Petersoj/FSSPrototype/assets/Schematics and PCB Layouts/Breakout Board v1.0/PCB Layers/Hole.pdf

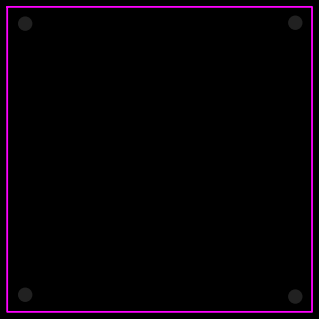
[picture p21: figure]
