Petersoj/FSSPrototype/assets/Schematics and PCB Layouts/Breakout Board v1.0/PCB Layers/Multi-Layer.pdf

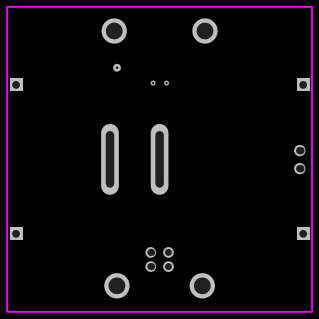
[picture p22: figure]
