Petersoj/FSSPrototype/assets/Schematics and PCB Layouts/Main Board v1.0/PCB Layers/Multi-Layer.pdf

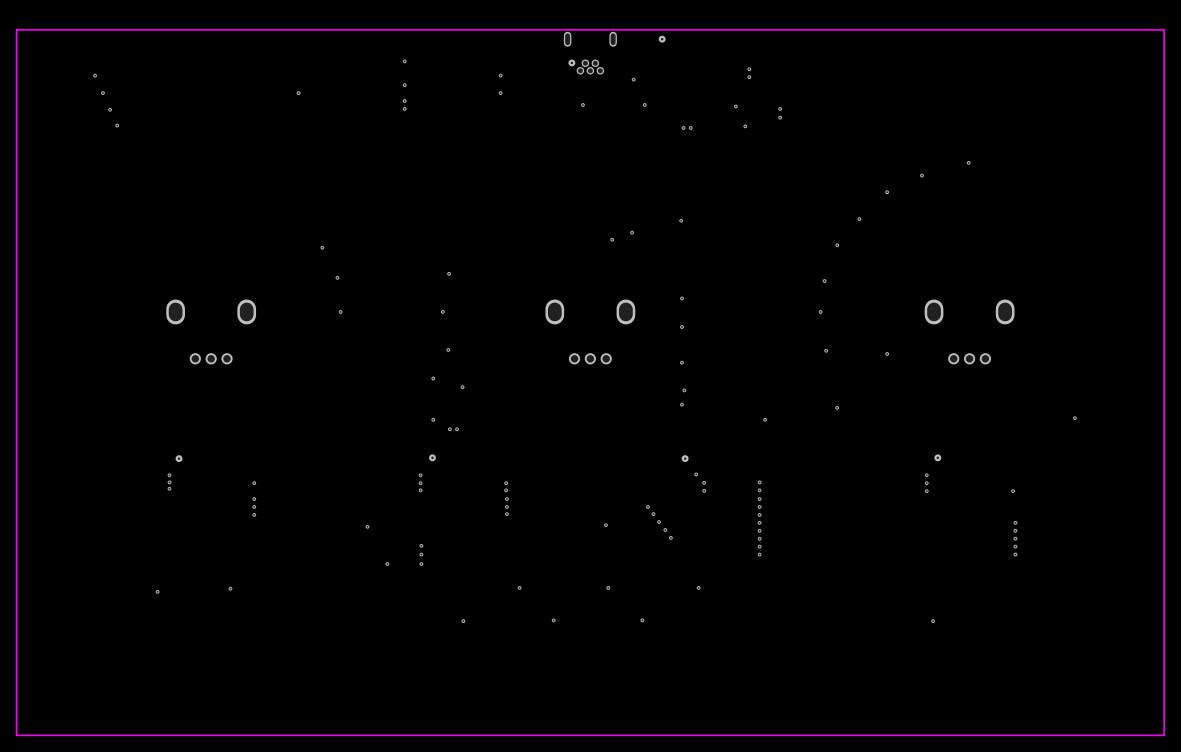
[picture p23: page 1]
