Petersoj/FSSPrototype/assets/Schematics and PCB Layouts/Main Board v1.0/PCB Layers/TopPasteMaskLayer.pdf

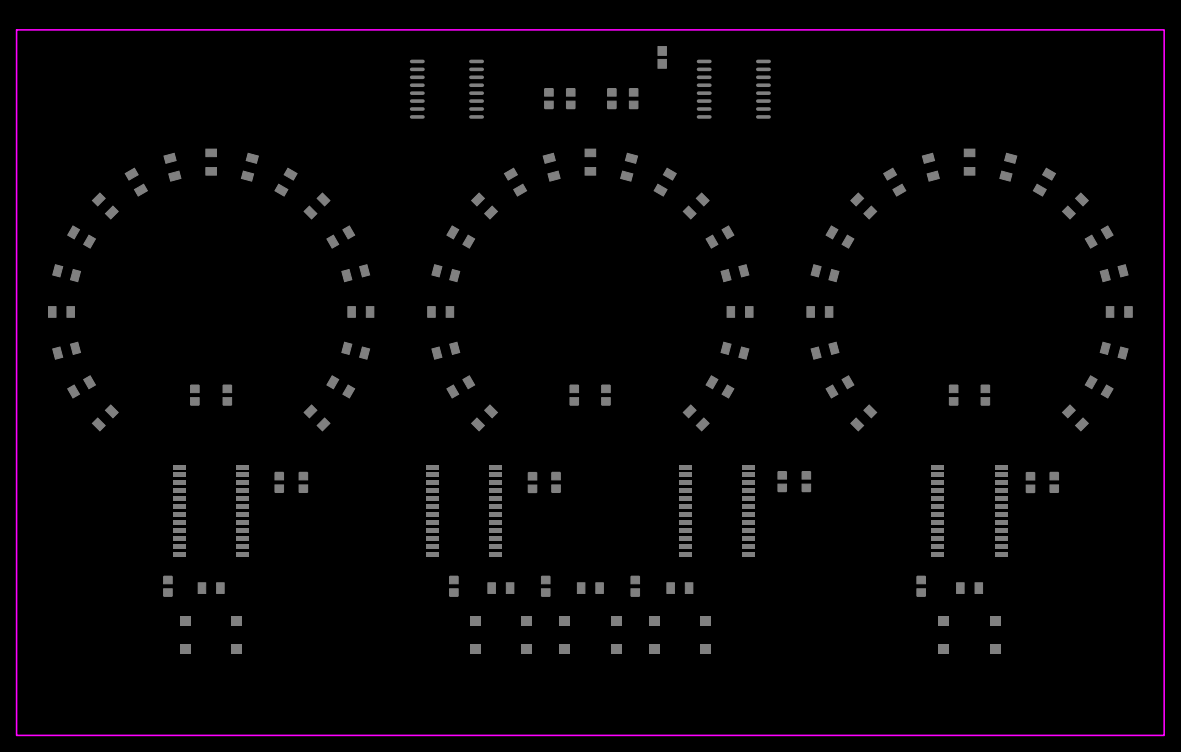
[picture p24: page 1]
