Petersoj/FSSPrototype/assets/Schematics and PCB Layouts/Breakout Board v1.0/PCB Layers/BottomSolderMaskLayer.pdf

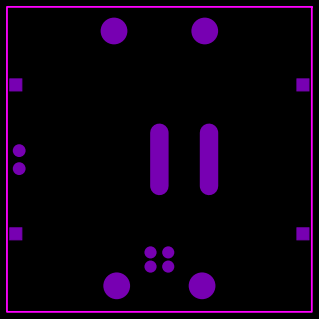
[picture p39: figure]
