Petersoj/FSSPrototype/assets/Schematics and PCB Layouts/Breakout Board v1.0/PCB Layers/TopSolderMaskLayer.pdf

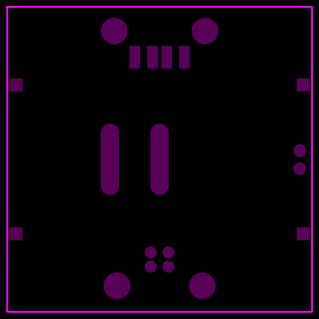
[picture p40: figure]
