Petersoj/FSSPrototype/assets/Schematics and PCB Layouts/Breakout Board v1.0/PCB Layers/BottomLayer.pdf

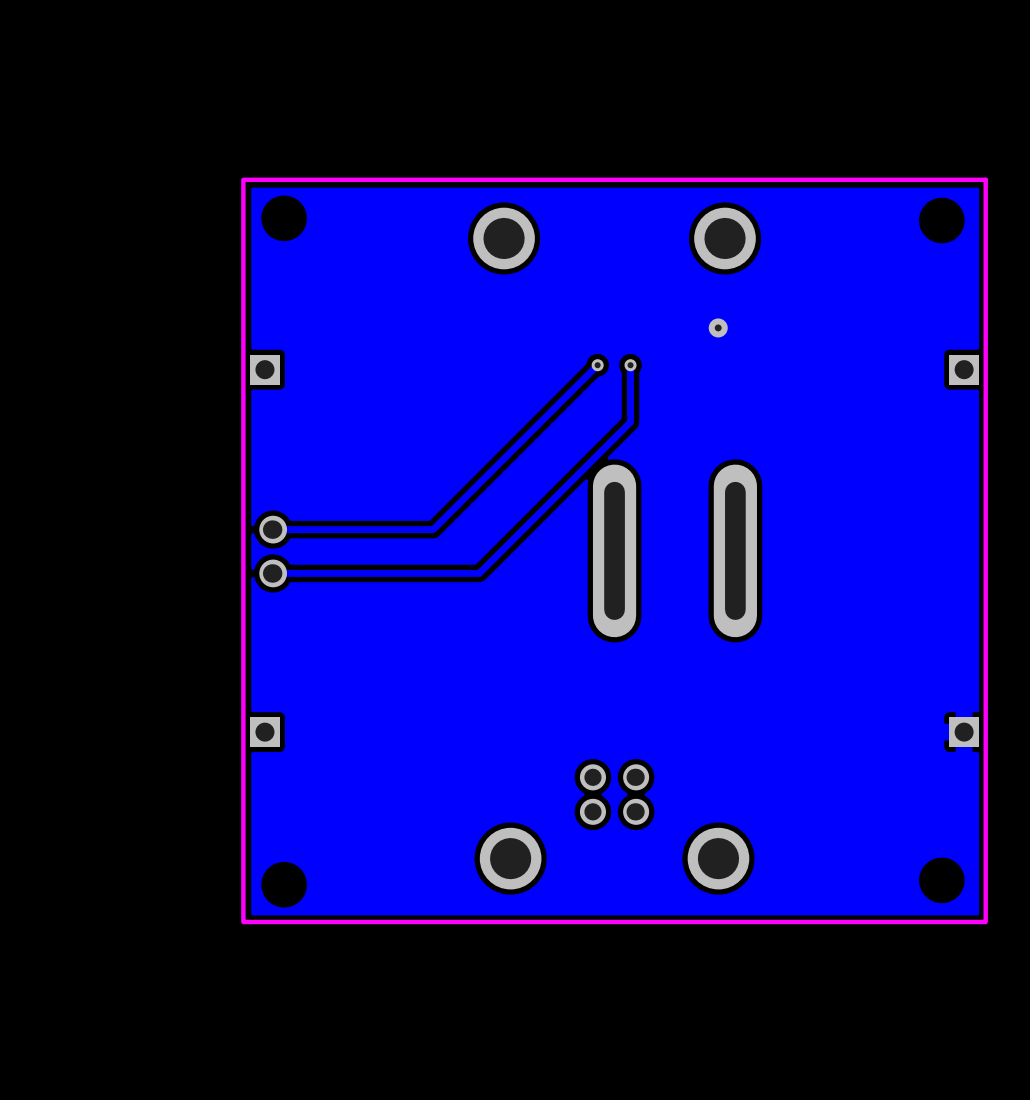
[picture p47: page 1]
