Petersoj/FSSPrototype/assets/Schematics and PCB Layouts/Breakout Board v1.0/PCB Layers/TopLayer.pdf

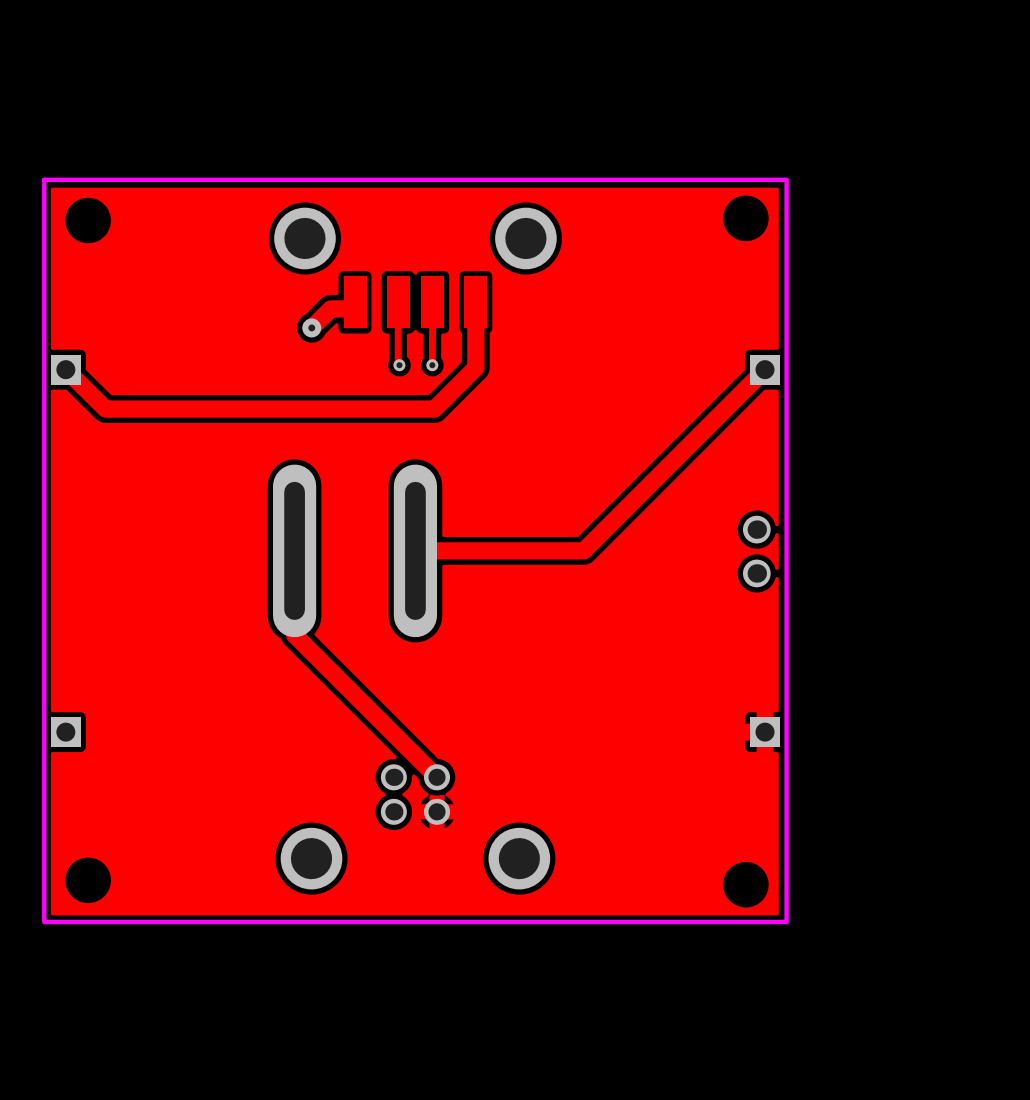
[picture p48: page 1]
