Petersoj/FSSPrototype/assets/Schematics and PCB Layouts/Breakout Board v1.0/PCB Layers/TopSilkLayer.pdf

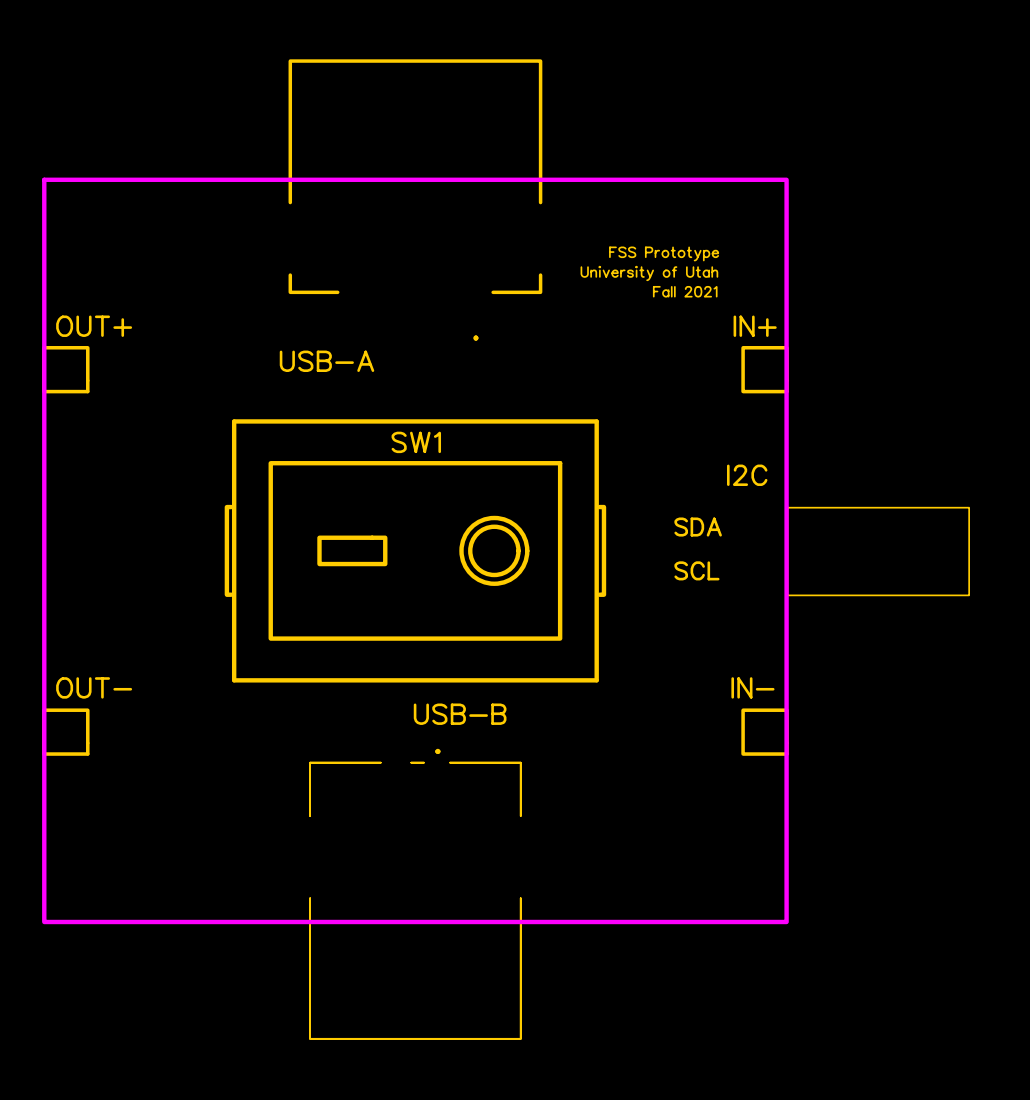
[picture p49: page 1]
