Petersoj/FSSPrototype/assets/Schematics and PCB Layouts/Main Board v1.0/PCB Layers/BottomLayer.pdf

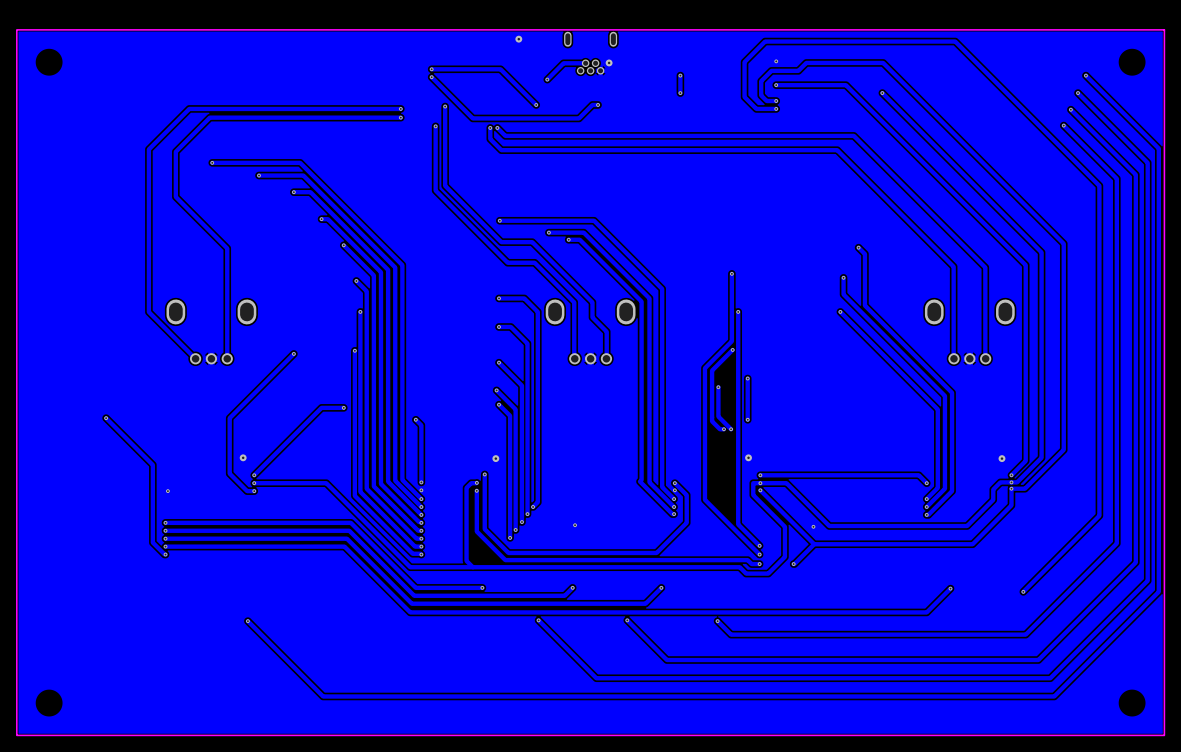
[picture p50: page 1]
