Petersoj/FSSPrototype/assets/Schematics and PCB Layouts/Main Board v1.0/PCB Layers/TopLayer.pdf

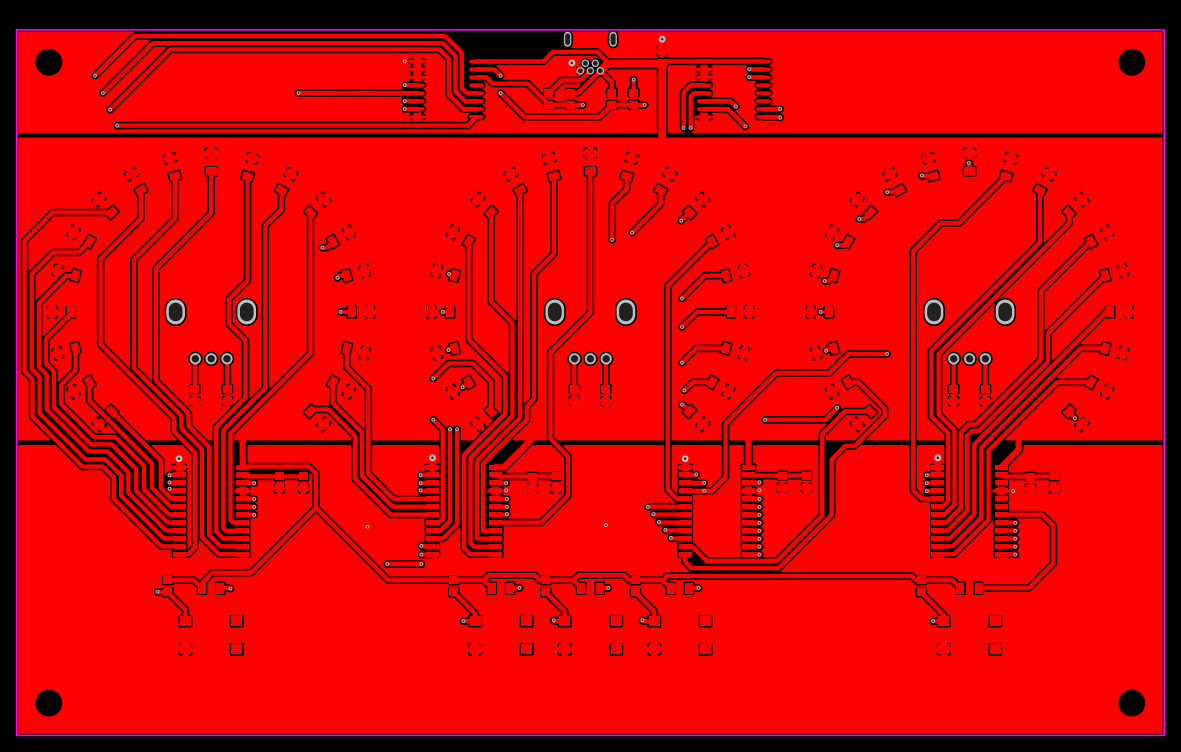
[picture p51: page 1]
