Petersoj/FSSPrototype/assets/Schematics and PCB Layouts/Main Board v1.0/PCB Layers/TopSilkLayer.pdf

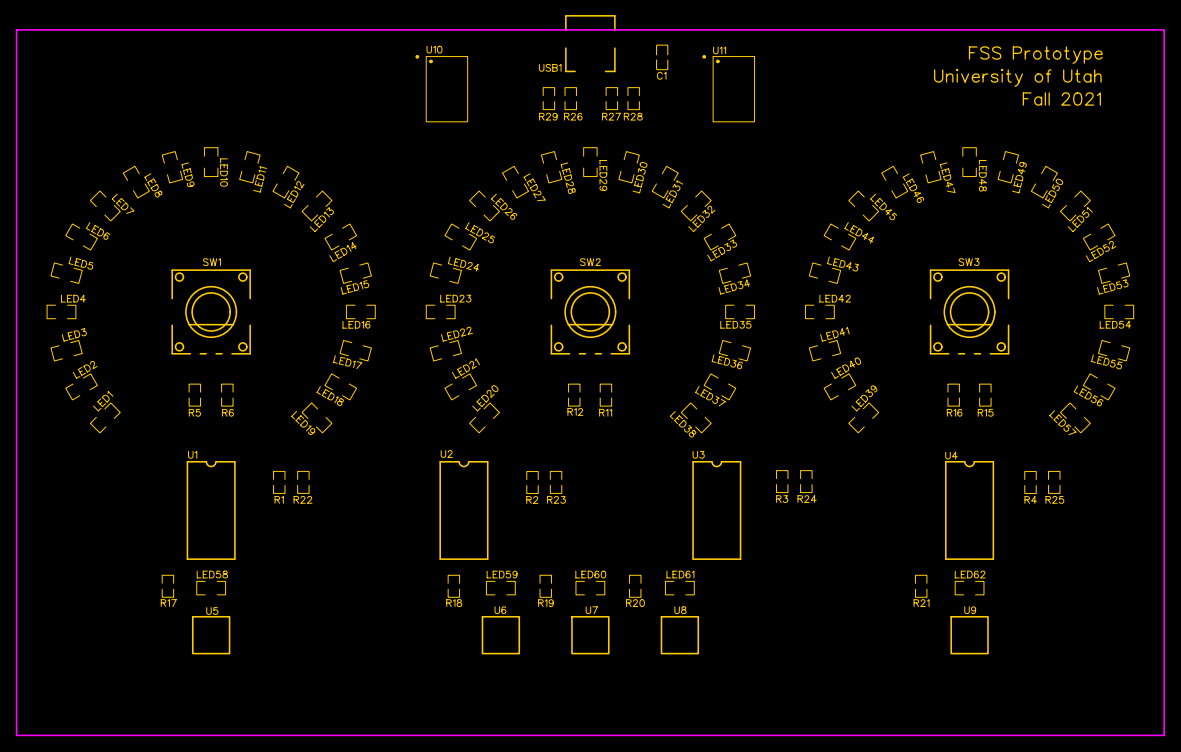
[picture p52: page 1]
