Petersoj/FSSPrototype/assets/Schematics and PCB Layouts/Main Board v1.0/PCB Layers/TopSolderMaskLayer.pdf

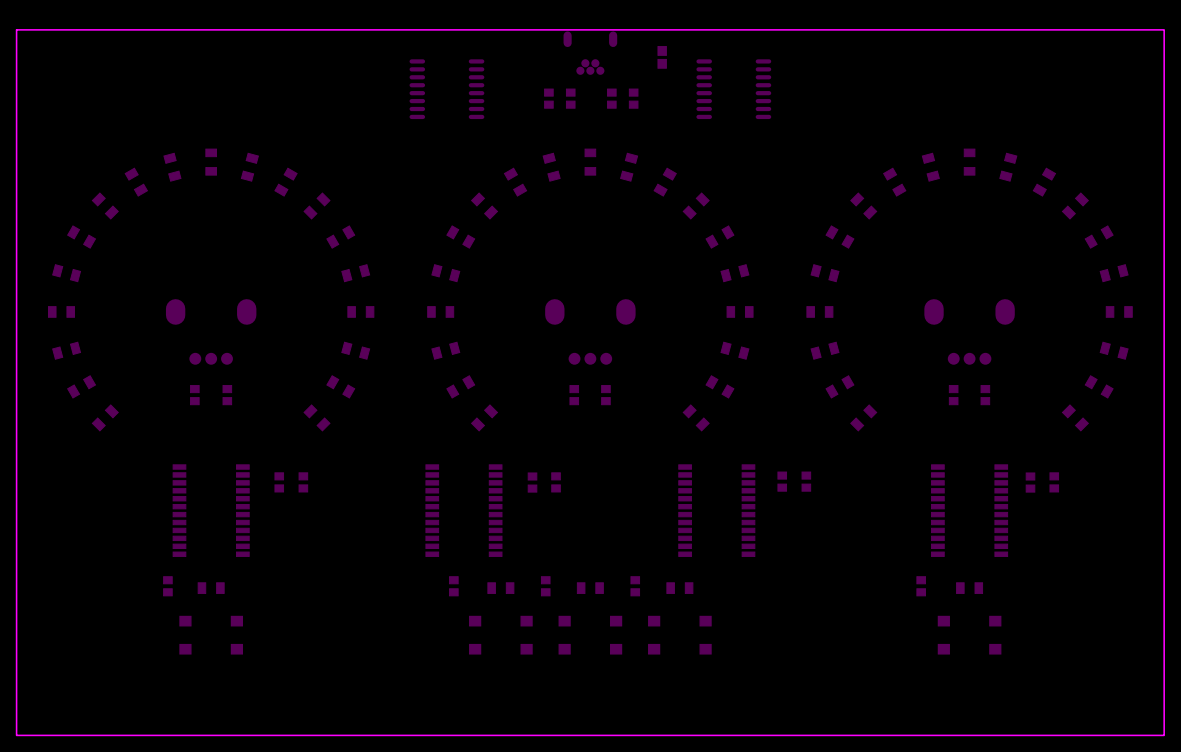
[picture p53: page 1]
