Petersoj/FSSPrototype/docs/Reports/Final Report/resources/figures/breakout_pcb.pdf

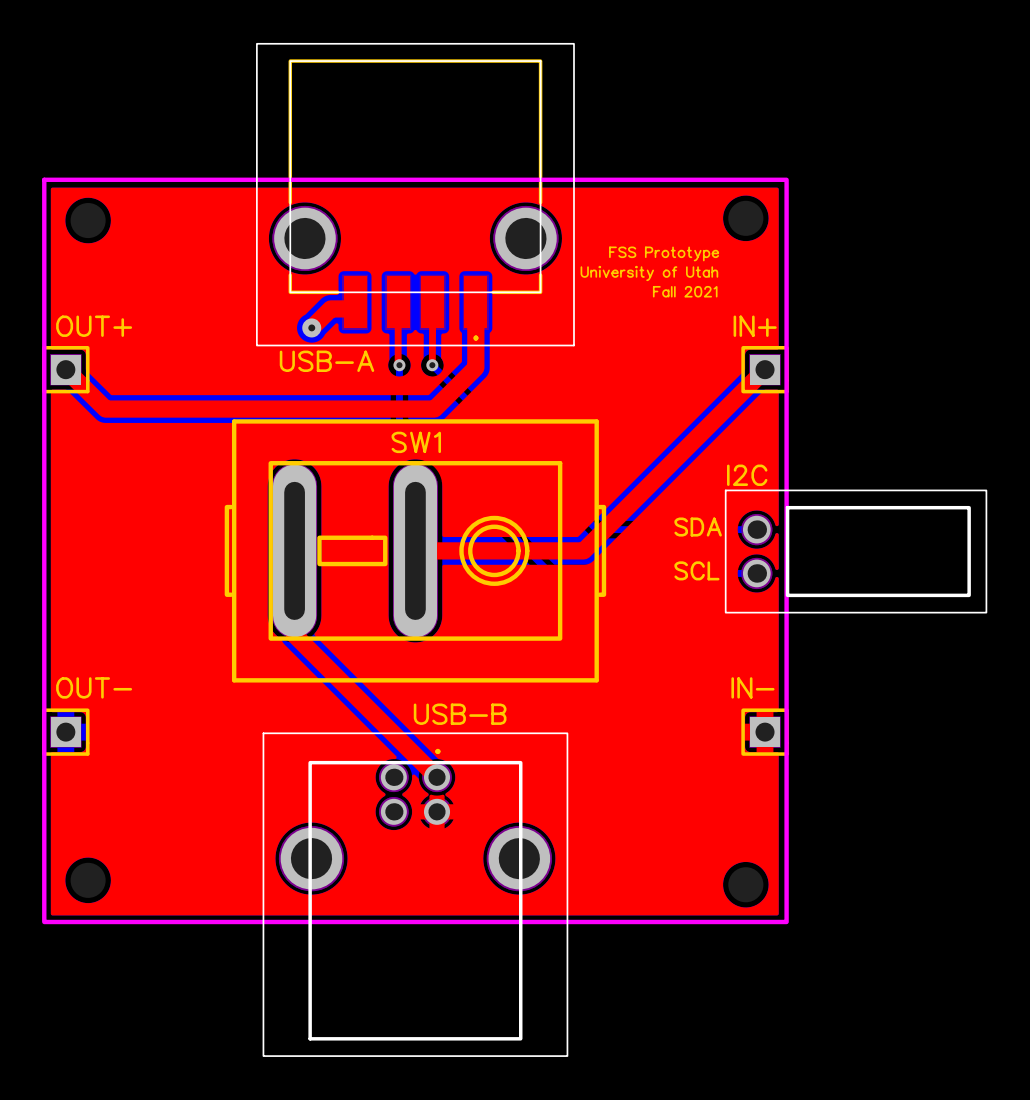
[picture p54: page 1]
