Petersoj/FSSPrototype/docs/Reports/Final Report/resources/figures/breakout_schematic.pdf

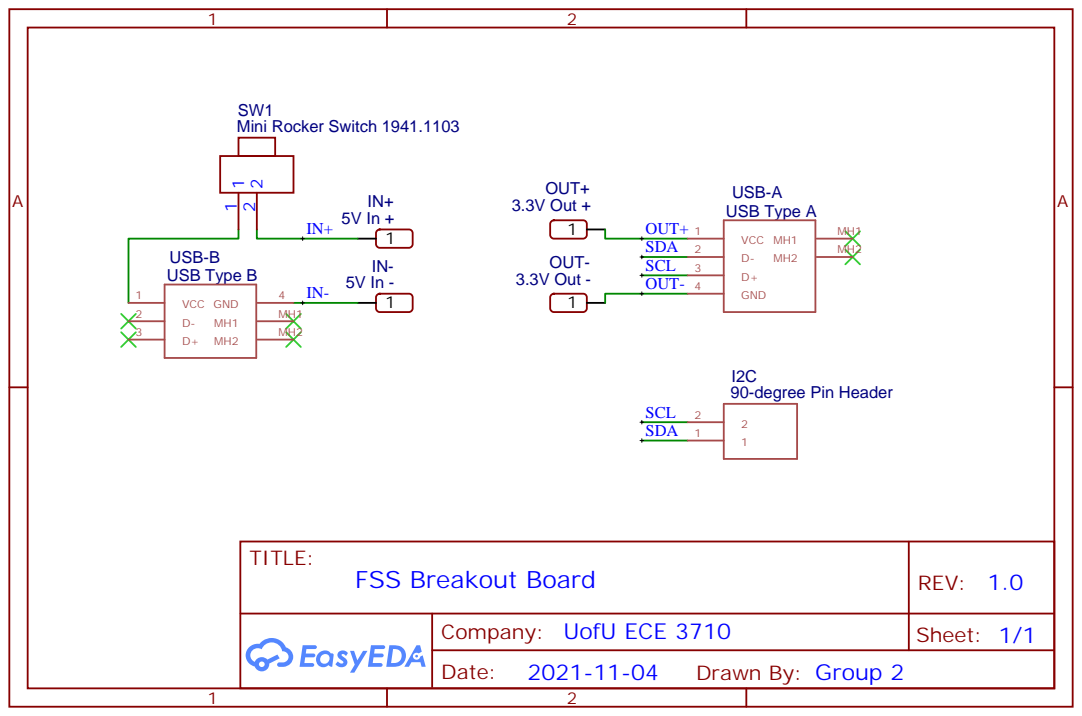
[picture p55: page 1]
