Petersoj/FSSPrototype/docs/Reports/Final Report/resources/figures/main_pcb.pdf

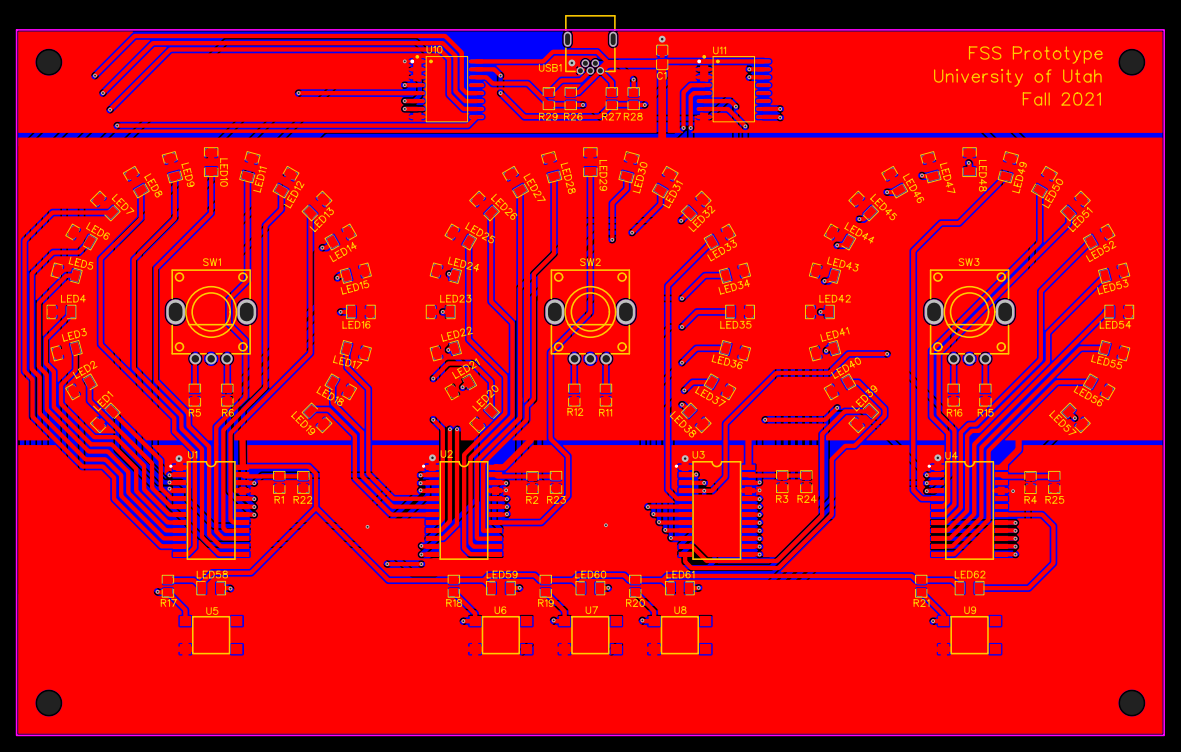
[picture p56: page 1]
