Petersoj/FSSPrototype/docs/Reports/Final Report/resources/figures/main_schematic.pdf

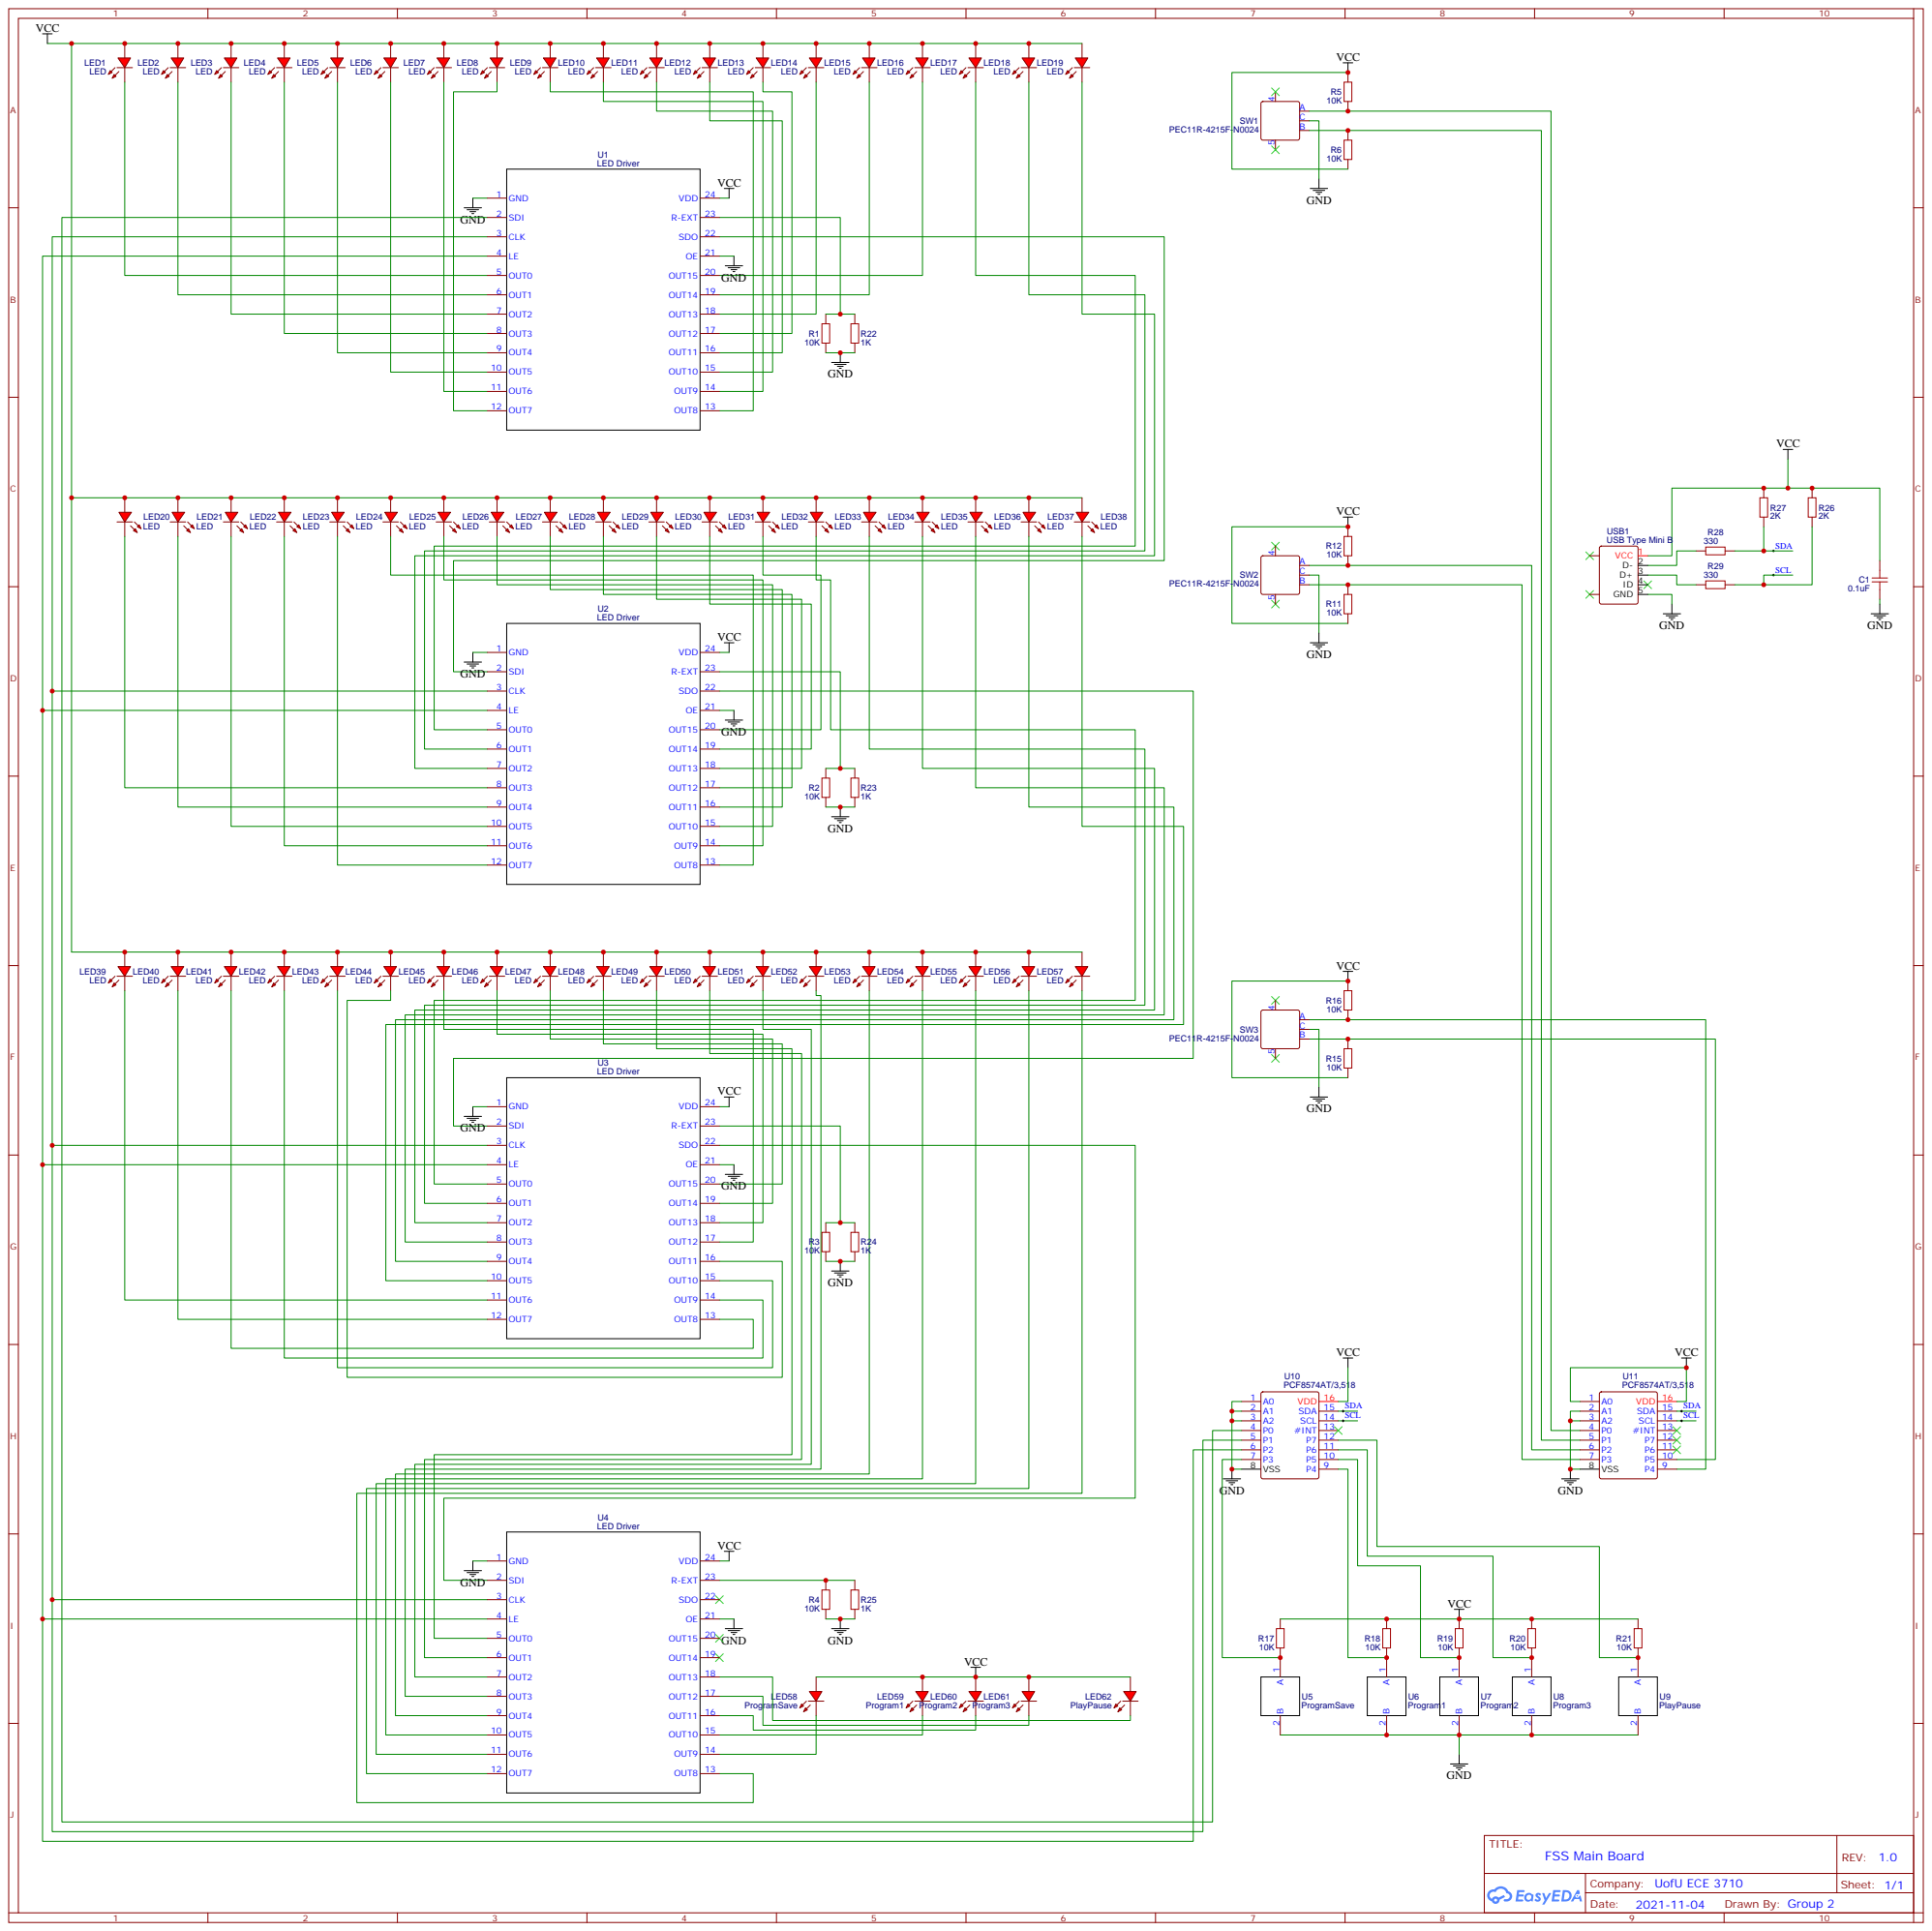
[picture p57: page 1]
